MasterSpoon/Ortho66_Optical/Ortho66_Optical.kicad_sch

## KiCad design Ortho66_Optical.kicad_sch (2022-03-05)

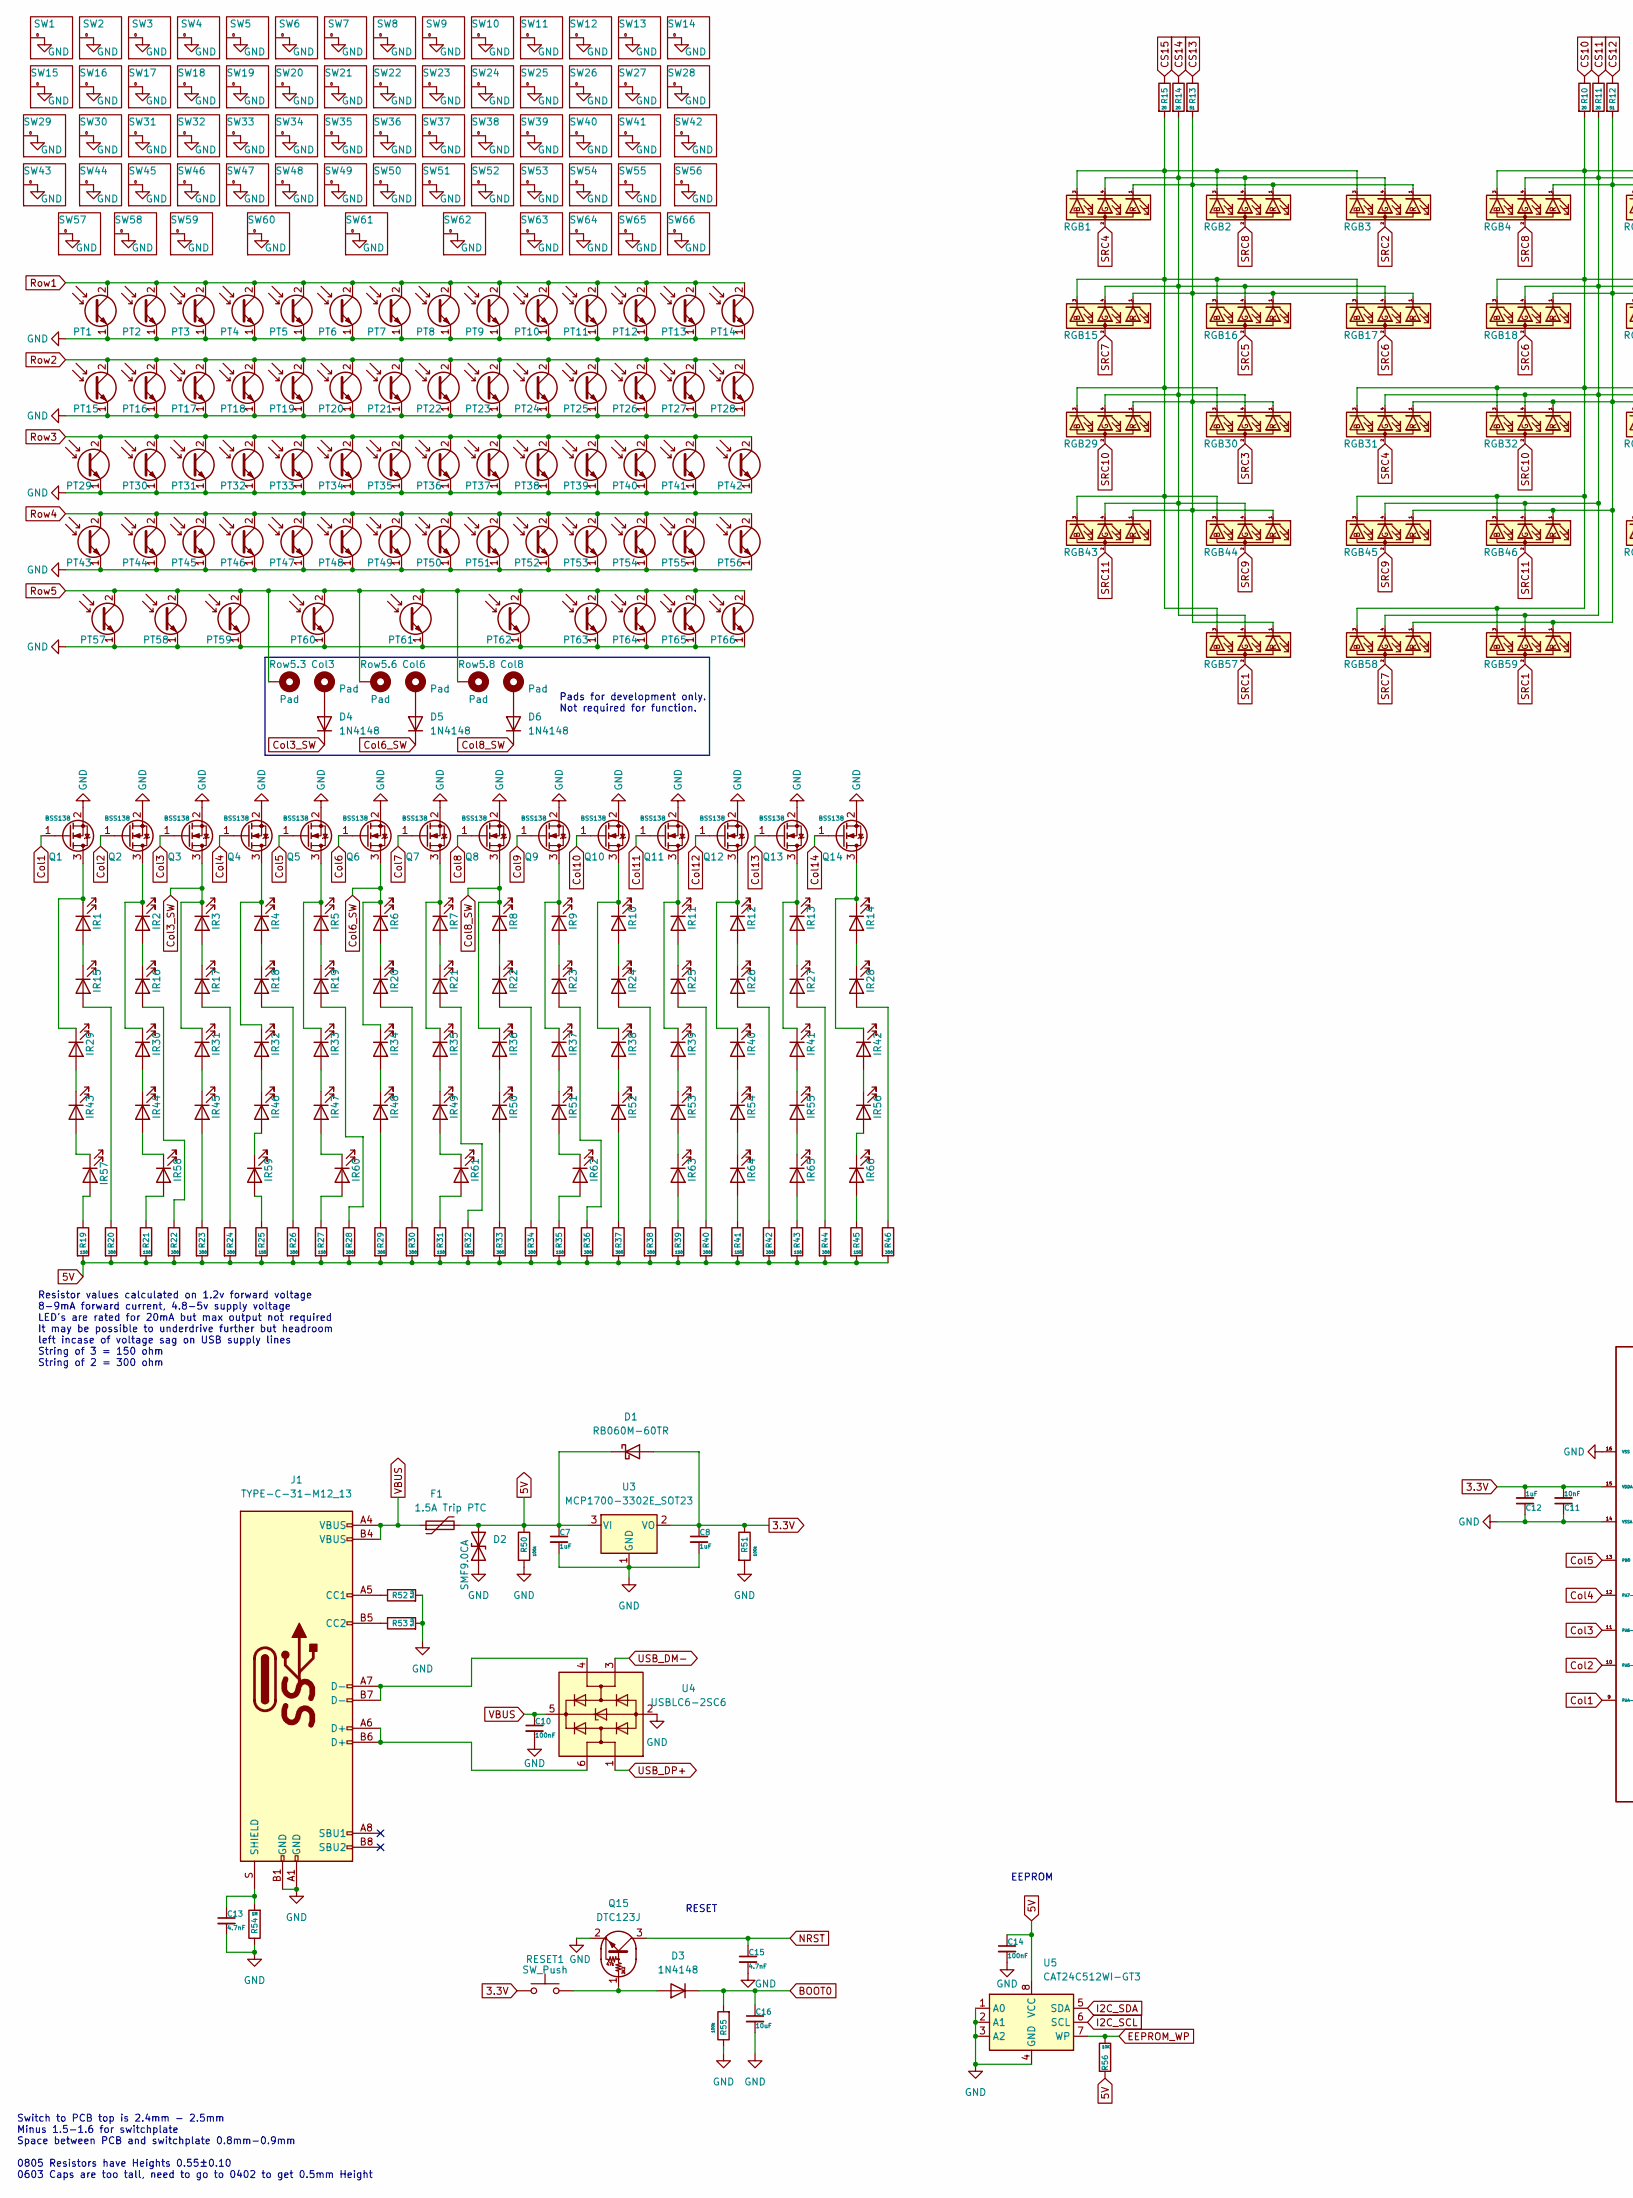
[picture p3: schematic Ortho66_Optical.kicad_sch, part in row 1, column 1]

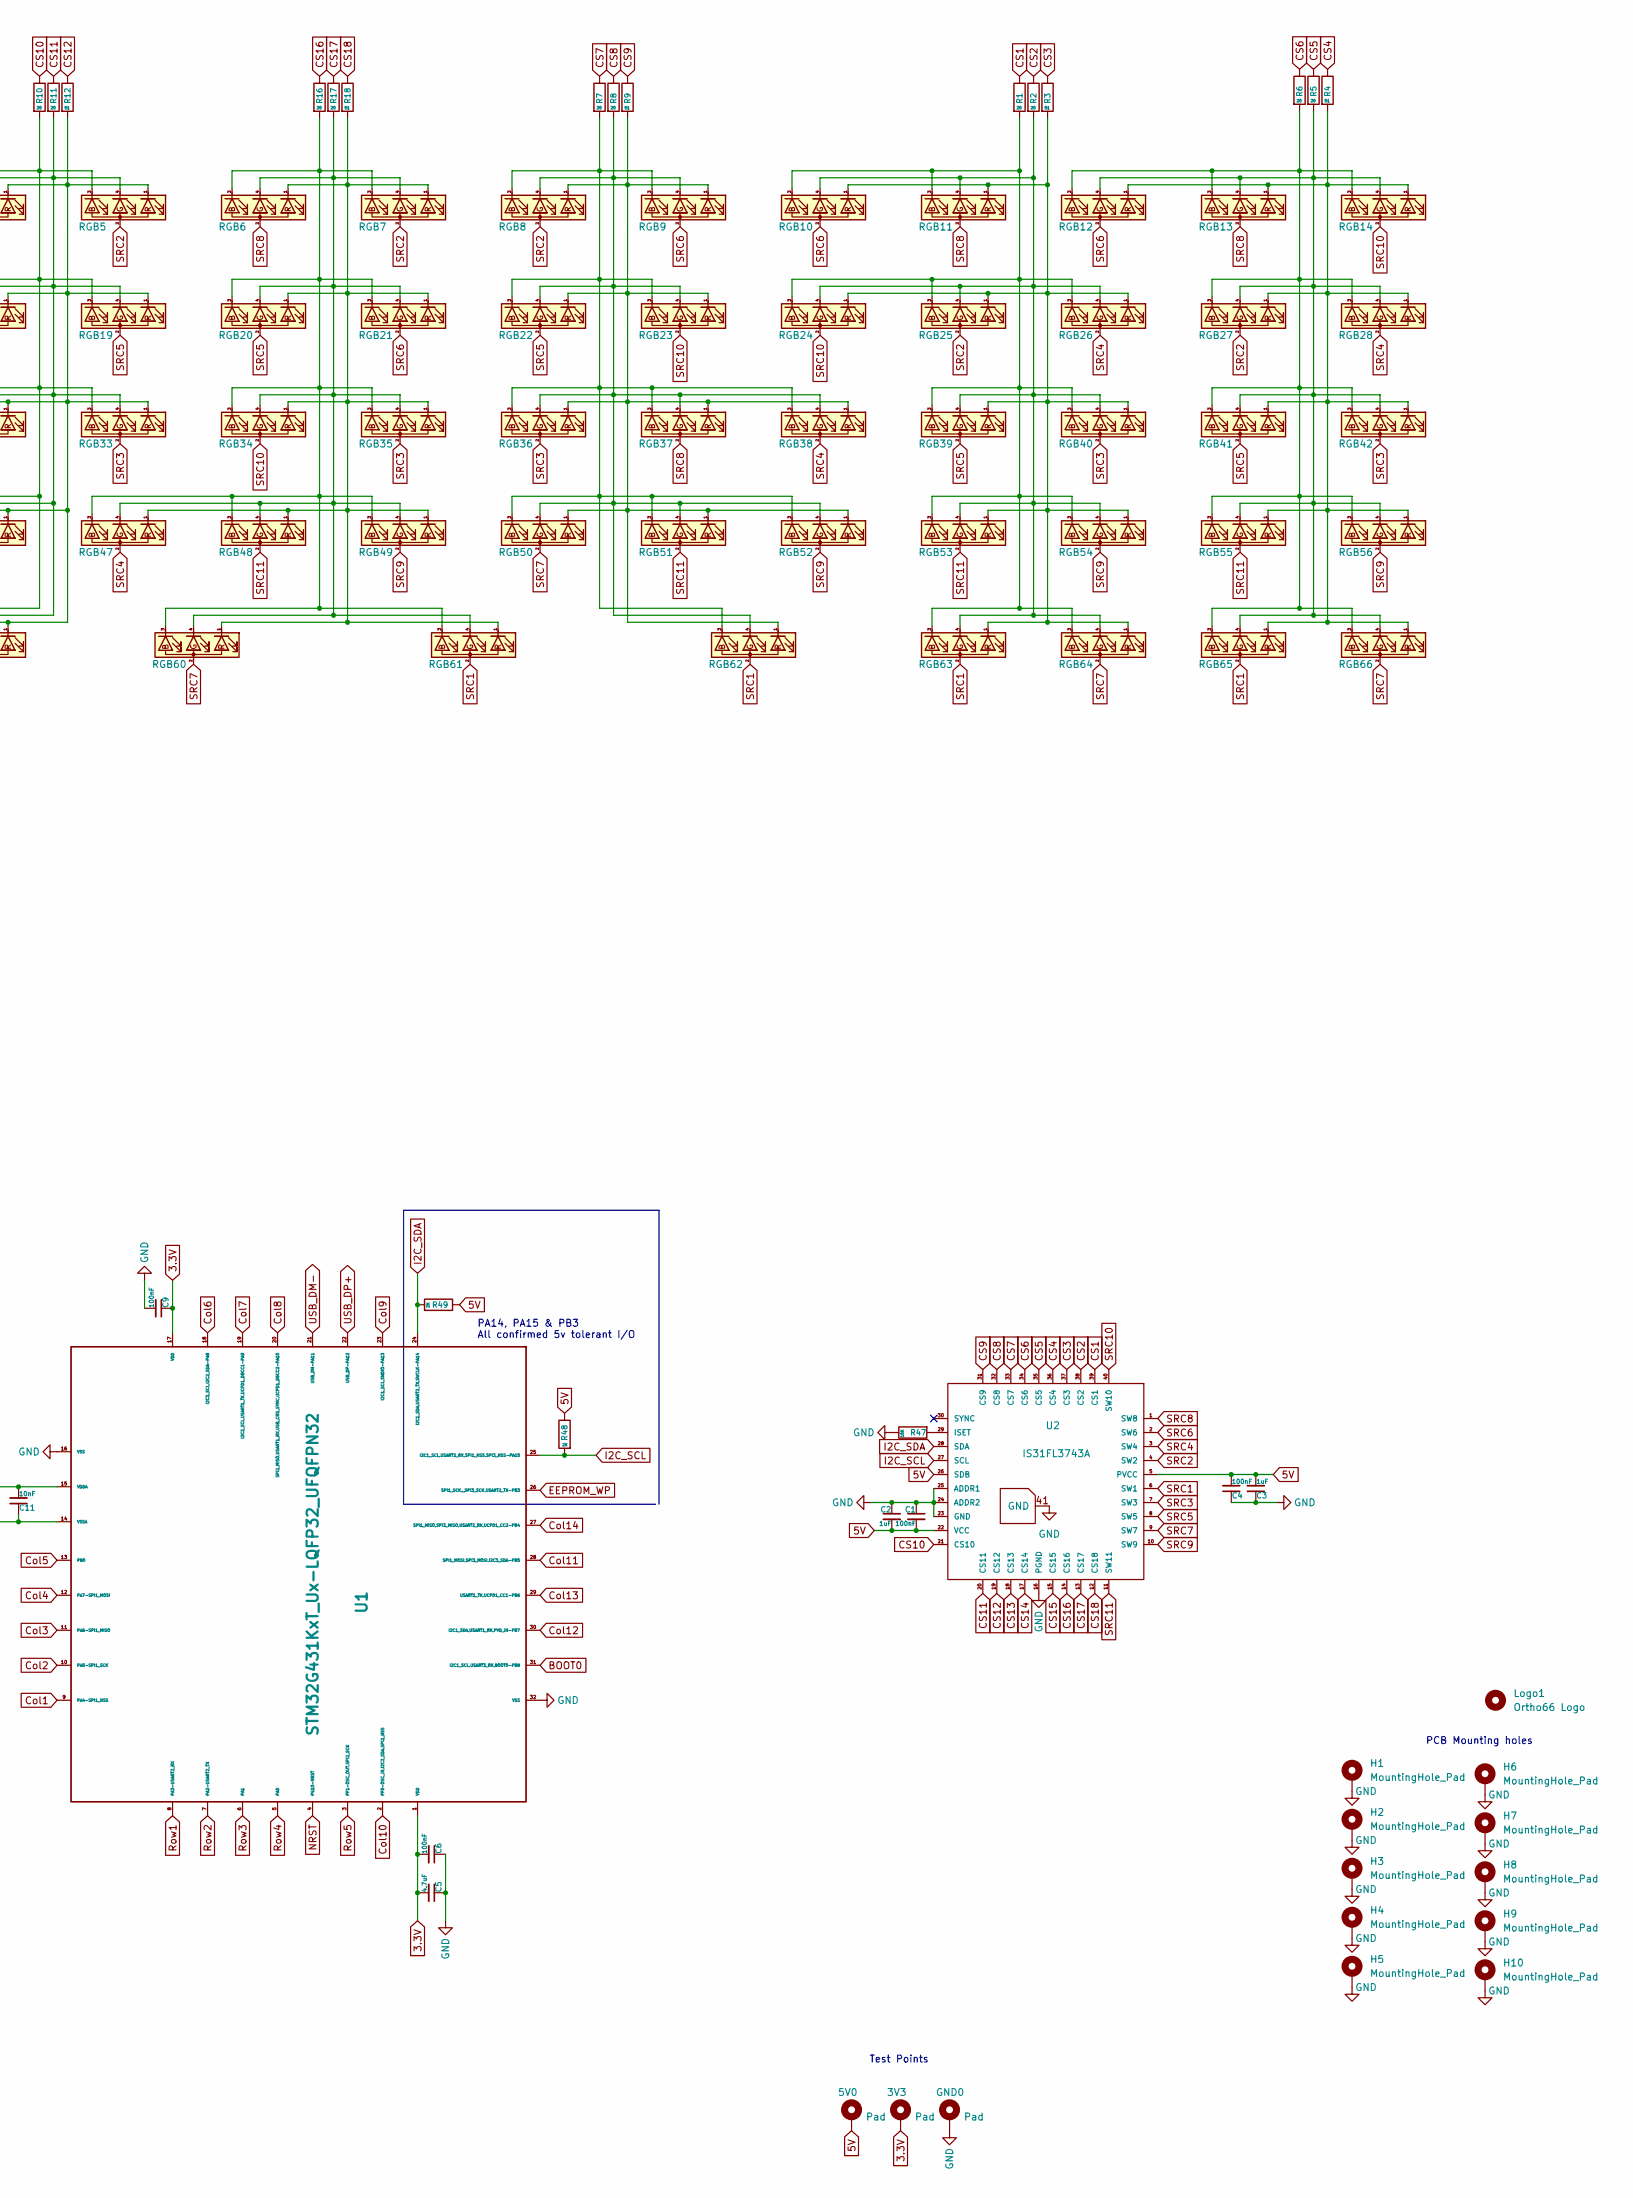
[picture p4: schematic Ortho66_Optical.kicad_sch, part in row 1, column 2]

Parts:
3V3, 5V0: Pad; SolderWirePad_1x01_SMD_1x2mm
C1, C4, C6, C9, C10, C14: 100nF; C_0402_1005Metric
C2, C3, C7, C8, C12: 1uF; C_0402_1005Metric
C5: 4.7uF; C_0402_1005Metric
C11: 10nF; C_0402_1005Metric
C13, C15: 4.7nF; C_0402_1005Metric
C16: 10uF; C_0402_1005Metric
Col3, Col6, Col8: Pad; SolderWirePad_1x01_SMD_1x2mm
D1: RB060M-60TR; D_SOD-123
D2: SMF9.0CA; D_SOD-123
D3, D4, D5, D6: 1N4148; D_SOD-123
F1: 1.5A Trip PTC; Fuse_1812_4532Metric
GND0: Pad; SolderWirePad_1x01_SMD_1x2mm
H1, H2, H3, H4, H5, H6, H7, H8, H9, H10: MountingHole_Pad; 6.2mm_mount
IR1, IR2, IR3, IR4, IR5, IR6, IR7, IR8, IR9, IR10, IR11, IR12, IR13, IR14, IR15, IR16, IR17, IR18, IR19, IR20, IR21, IR22, IR23, IR24, IR25, IR26, IR27, IR28, IR29, IR30, IR31, IR32, IR33, IR34, IR35, IR36, IR37, IR38, IR39, IR40, IR41, IR42, IR43, IR44, IR45, IR46, IR47, IR48, IR49, IR50, IR51, IR52, IR53, IR54, IR55, IR56, IR57, IR58, IR59, IR60, IR61, IR62, IR63, IR64, IR65, IR66: IR12-21C_TR8; LCSC C53672
J1: TYPE-C-31-M12_13; USB_C_Receptacle_TYPE-C-31-M-12
Logo1: Ortho66 Logo; Ortho_66_Logo
PT1, PT2, PT3, PT4, PT5, PT6, PT7, PT8, PT9, PT10, PT11, PT12, PT13, PT14, PT15, PT16, PT17, PT18, PT19, PT20, PT21, PT22, PT23, PT24, PT25, PT26, PT27, PT28, PT29, PT30, PT31, PT32, PT33, PT34, PT35, PT36, PT37, PT38, PT39, PT40, PT41, PT42, PT43, PT44, PT45, PT46, PT47, PT48, PT49, PT50, PT51, PT52, PT53, PT54, PT55, PT56, PT57, PT58, PT59, PT60, PT61, PT62, PT63, PT64, PT65, PT66: PT12-21B_TR8; LCSC C264383
Q1, Q2, Q3, Q4, Q5, Q6, Q7, Q8, Q9, Q10, Q11, Q12, Q13, Q14: BSS138; SOT-23
Q15: DTC123J; SOT-23
R1, R2, R5, R6, R7, R8, R10, R11, R14, R15, R16, R17: 20; R_0805_2012Metric
R3, R4, R9, R12, R13, R18: 51; R_0805_2012Metric
R19, R21, R25, R27, R31, R35, R39, R41, R43, R45: 150; R_0805_2012Metric
R20, R22, R23, R24, R26, R28, R29, R30, R32, R33, R34, R36, R37, R38, R40, R42, R44, R46: 300; R_0805_2012Metric
R47, R56: 10K; R_0805_2012Metric
R48, R49: 2K; R_0805_2012Metric
R50, R51, R55: 100k; R_0805_2012Metric
R52, R53: 5.1k; R_0805_2012Metric
R54: 1M; R_0805_2012Metric
RESET1: SW_Push; K2-1187SQ-A4SW-06
RGB1, RGB2, RGB4, RGB6, RGB9, RGB10, RGB13, RGB26, RGB31, RGB47: RS-1515MBAM; RS-1515MBAM-RGB_LED-TopRight; LCSC C727906
RGB3, RGB5, RGB7, RGB11, RGB14: RS-1515MBAM; RS-1515MBAM-RGB_LED-TopLeft; LCSC C727906
RGB8, RGB38: RS-1515MBAM; RS-1515MBAM-RGB_LED-Top; LCSC C727906
RGB12: RS-1515MBAM; RS-1515MBAM-RGB_LED-SW12; LCSC C727906
RGB15, RGB16, RGB18, RGB19, RGB20, RGB21, RGB22, RGB23, RGB25, RGB27, RGB30, RGB32, RGB34, RGB35, RGB36, RGB37, RGB39, RGB40, RGB41, RGB42, RGB46, RGB51, RGB53, RGB54, RGB55, RGB56: RS-1515MBAM; RS-1515MBAM-RGB_LED-Midjoin; LCSC C727906
RGB17, RGB24, RGB33, RGB64, RGB65: RS-1515MBAM; RS-1515MBAM-RGB_LED-Bott; LCSC C727906
RGB28: RS-1515MBAM; RS-1515MBAM-RGB_LED-SW28; LCSC C727906
RGB29: RS-1515MBAM; RS-1515MBAM-RGB_LED-SW29; LCSC C727906
RGB43, RGB49, RGB50: RS-1515MBAM; RS-1515MBAM-RGB_LED-Bottjoinleft; LCSC C727906
RGB44, RGB63: RS-1515MBAM; RS-1515MBAM-RGB_LED-SW63; LCSC C727906
RGB45, RGB48, RGB52: RS-1515MBAM; RS-1515MBAM-RGB_LED-Bottjoinright; LCSC C727906
RGB57, RGB61: RS-1515MBAM; RS-1515MBAM-RGB_LED-Bottleft; LCSC C727906
RGB58, RGB60, RGB62: RS-1515MBAM; RS-1515MBAM-RGB_LED-Bottright; LCSC C727906
RGB59, RGB66: RS-1515MBAM; RS-1515MBAM-RGB_LED-SW66; LCSC C727906
Row5.3, Row5.6, Row5.8: Pad; SolderWirePad_1x01_SMD_1x2mm
SW1, SW2, SW3, SW4, SW5, SW6, SW7, SW8, SW9, SW10, SW11, SW12, SW13, SW14, SW15, SW16, SW17, SW18, SW19, SW20, SW21, SW22, SW23, SW24, SW25, SW26, SW27, SW28, SW29, SW30, SW31, SW32, SW33, SW34, SW35, SW36, SW37, SW38, SW39, SW40, SW41, SW42, SW43, SW44, SW45, SW46, SW47, SW48, SW49, SW50, SW51, SW52, SW53, SW54, SW55, SW56, SW57, SW58, SW59, SW60, SW61, SW62, SW63, SW64, SW65, SW66: Keychron_LP_Optical
U1: STM32G431KxT_Ux-LQFP32_UFQFPN32; LQFP-32_7x7mm_P0.8mm
U2: IS31FL3743A; QFN-40-IS31FL3743A_0.2mmClearance
U3: MCP1700-3302E_SOT23; SOT-23
U4: USBLC6-2SC6; SOT-23-6
U5: CAT24C512WI-GT3; SOIC-8_5.23x5.23mm_P1.27mm; LCSC C79986

Connections:
3.3V: 3V3.1, C5.2, C6.2, C8.1, C9.1, C11.2, C12.2, D1.2 (A), R51.1, RESET1.2, U1.1 (VDD), U1.15 (VDDA), U1.17 (VDD), U3.2 (VO)
5V: 5V0.1, C1.2, C2.2, C3.2, C4.2, C7.1, C14.1, D1.1 (K), D2.2 (A2), F1.2, R19.2, R20.2, R21.2, R22.2, R23.2, R24.2, R25.2, R26.2, R27.2, R28.2, R29.2, R30.2, R31.2, R32.2, R33.2, R34.2, R35.2, R36.2, R37.2, R38.2, R39.2, R40.2, R41.2, R42.2, R43.2, R44.2, R45.2, R46.2, R48.1, R49.1, R50.1, R56.2, U2.5 (PVCC), U2.22 (VCC), U2.26 (SDB), U3.3 (VI), U5.8 (VCC)
BOOT0: C16.1, D3.1 (K), R55.2, U1.31 (I2C1_SCL,USART3_RX,BOOT0-PB8)
CS1: R1.1, U2.39 (CS1)
CS2: R2.1, U2.38 (CS2)
CS3: R3.1, U2.37 (CS3)
CS4: R4.1, U2.36 (CS4)
CS5: R5.1, U2.35 (CS5)
CS6: R6.1, U2.34 (CS6)
CS7: R7.1, U2.33 (CS7)
CS8: R8.1, U2.32 (CS8)
CS9: R9.1, U2.31 (CS9)
CS10: R10.1, U2.21 (CS10)
CS11: R11.1, U2.20 (CS11)
CS12: R12.1, U2.19 (CS12)
CS13: R13.1, U2.18 (CS13)
CS14: R14.1, U2.17 (CS14)
CS15: R15.1, U2.15 (CS15)
CS16: R16.1, U2.14 (CS16)
CS17: R17.1, U2.13 (CS17)
CS18: R18.1, U2.12 (CS18)
Col1: Q1.1 (G), U1.9 (PA4-SPI1_NSS)
Col2: Q2.1 (G), U1.10 (PA5-SPI1_SCK)
Col3: Q3.1 (G), U1.11 (PA6-SPI1_MISO)
Col3_SW: D4.1 (K), IR3.2 (K), IR31.2 (K), Q3.3 (D)
Col4: Q4.1 (G), U1.12 (PA7-SPI1_MOSI)
Col5: Q5.1 (G), U1.13 (PB0)
Col6: Q6.1 (G), U1.18 (I2C3_SCL,I2C2_SDA-PA8)
Col6_SW: D5.1 (K), IR6.2 (K), IR34.2 (K), Q6.3 (D)
Col7: Q7.1 (G), U1.19 (I2C2_SCL,USART1_TX,UCPD1_DBCC1-PA9)
Col8: Q8.1 (G), U1.20 (SPI2_MISO,USART1_RX,USB_CRS_SYNC,UCPD1_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)
Col8_SW: D6.1 (K), IR8.2 (K), IR36.2 (K), Q8.3 (D)
Col9: Q9.1 (G), U1.23 (I2C1_SCL,SWDIO-PA13)
Col10: Q10.1 (G), U1.2 (PF0-OSC_IN,I2C2_SDA,SPI2_NSS)
Col11: Q11.1 (G), U1.28 (SPI1_MOSI,SPI3_MOSI,I2C3_SDA-PB5)
Col12: Q12.1 (G), U1.30 (I2C1_SDA,USART1_RX,PVD_IN-PB7)
Col13: Q13.1 (G), U1.29 (USART1_TX,UCPD1_CC1-PB6)
Col14: Q14.1 (G), U1.27 (SPI1_MISO,SPI3_MISO,USART2_RX,UCPD1_CC2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)
EEPROM_WP: R56.1, U1.26 (SPI1_SCK,_SPI3_SCK,USART2_TX-PB3), U5.7 (WP)
GND: C1.1, C2.1, C3.1, C4.1, C5.1, C6.1, C7.2, C8.2, C9.2, C10.2, C11.1, C12.1, C13.2, C14.2, C15.2, C16.2, D2.1 (A1), H1.0, H2.0, H3.0, H4.0, H5.0, H6.0, H7.0, H8.0, H9.0, H10.0, J1.A1 (GND), J1.B1 (GND), PT1.1 (E), PT2.1 (E), PT3.1 (E), PT4.1 (E), PT5.1 (E), PT6.1 (E), PT7.1 (E), PT8.1 (E), PT9.1 (E), PT10.1 (E), PT11.1 (E), PT12.1 (E), PT13.1 (E), PT14.1 (E), PT15.1 (E), PT16.1 (E), PT17.1 (E), PT18.1 (E), PT19.1 (E), PT20.1 (E), PT21.1 (E), PT22.1 (E), PT23.1 (E), PT24.1 (E), PT25.1 (E), PT26.1 (E), PT27.1 (E), PT28.1 (E), PT29.1 (E), PT30.1 (E), PT31.1 (E), PT32.1 (E), PT33.1 (E), PT34.1 (E), PT35.1 (E), PT36.1 (E), PT37.1 (E), PT38.1 (E), PT39.1 (E), PT40.1 (E), PT41.1 (E), PT42.1 (E), PT43.1 (E), PT44.1 (E), PT45.1 (E), PT46.1 (E), PT47.1 (E), PT48.1 (E), PT49.1 (E), PT50.1 (E), PT51.1 (E), PT52.1 (E), PT53.1 (E), PT54.1 (E), PT55.1 (E), PT56.1 (E), PT57.1 (E), PT58.1 (E), PT59.1 (E), PT60.1 (E), PT61.1 (E), PT62.1 (E), PT63.1 (E), PT64.1 (E), PT65.1 (E), PT66.1 (E), Q1.2 (S), Q2.2 (S), Q3.2 (S), Q4.2 (S), Q5.2 (S), Q6.2 (S), Q7.2 (S), Q8.2 (S), Q9.2 (S), Q10.2 (S), Q11.2 (S), Q12.2 (S), Q13.2 (S), Q14.2 (S), Q15.2 (E), R47.1, R50.2, R51.2, R52.2, R53.2, R54.1, R55.1, SW1.0, SW2.0, SW3.0, SW4.0, SW5.0, SW6.0, SW7.0, SW8.0, SW9.0, SW10.0, SW11.0, SW12.0, SW13.0, SW14.0, SW15.0, SW16.0, SW17.0, SW18.0, SW19.0, SW20.0, SW21.0, SW22.0, SW23.0, SW24.0, SW25.0, SW26.0, SW27.0, SW28.0, SW29.0, SW30.0, SW31.0, SW32.0, SW33.0, SW34.0, SW35.0, SW36.0, SW37.0, SW38.0, SW39.0, SW40.0, SW41.0, SW42.0, SW43.0, SW44.0, SW45.0, SW46.0, SW47.0, SW48.0, SW49.0, SW50.0, SW51.0, SW52.0, SW53.0, SW54.0, SW55.0, SW56.0, SW57.0, SW58.0, SW59.0, SW60.0, SW61.0, SW62.0, SW63.0, SW64.0, SW65.0, SW66.0, U1.14 (VSSA), U1.16 (VSS), U1.32 (VSS), U2.16 (PGND), U2.23 (GND), U2.24 (ADDR2), U2.25 (ADDR1), U2.41 (GND), U3.1 (GND), U4.2 (GND), U5.1 (A0), U5.2 (A1), U5.3 (A2), U5.4 (GND)
I2C_SCL: R48.2, U1.25 (I2C1_SCL,USART2_RX,SPI1_NSS,SPI3_NSS-PA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), U2.27 (SCL), U5.6 (SCL)
I2C_SDA: R49.2, U1.24 (I2C1_SDA,USART2_TX,SWCLK-PA14), U2.28 (SDA), U5.5 (SDA)
NRST: C15.1, Q15.3 (C), U1.4 (PG10-NRST)
unnamed: C13.1, J1.S (SHIELD), R54.2
unnamed: Col3.1, D4.2 (A)
unnamed: Col6.1, D5.2 (A)
unnamed: Col8.1, D6.2 (A)
unnamed: D3.2 (A), Q15.1 (B), RESET1.1
unnamed: IR1.1 (A), IR15.2 (K)
unnamed: IR1.2 (K), IR29.2 (K), Q1.3 (D)
unnamed: IR2.2 (K), IR30.2 (K), Q2.3 (D)
unnamed: IR10.1 (A), IR24.2 (K)
unnamed: IR10.2 (K), IR38.2 (K), Q10.3 (D)
unnamed: IR11.1 (A), IR25.2 (K)
unnamed: IR11.2 (K), IR39.2 (K), Q11.3 (D)
unnamed: IR12.1 (A), IR26.2 (K)
unnamed: IR12.2 (K), IR40.2 (K), Q12.3 (D)
unnamed: IR13.1 (A), IR27.2 (K)
unnamed: IR13.2 (K), IR41.2 (K), Q13.3 (D)
unnamed: IR14.1 (A), IR28.2 (K)
unnamed: IR14.2 (K), IR42.2 (K), Q14.3 (D)
unnamed: IR15.1 (A), R20.1
unnamed: IR16.1 (A), R22.1
unnamed: IR2.1 (A), IR16.2 (K)
unnamed: IR17.1 (A), R24.1
unnamed: IR3.1 (A), IR17.2 (K)
unnamed: IR18.1 (A), R26.1
unnamed: IR4.1 (A), IR18.2 (K)
unnamed: IR19.1 (A), R28.1
unnamed: IR5.1 (A), IR19.2 (K)
unnamed: IR20.1 (A), R30.1
unnamed: IR6.1 (A), IR20.2 (K)
unnamed: IR21.1 (A), R32.1
unnamed: IR7.1 (A), IR21.2 (K)
unnamed: IR22.1 (A), R34.1
unnamed: IR8.1 (A), IR22.2 (K)
unnamed: IR23.1 (A), R36.1
unnamed: IR9.1 (A), IR23.2 (K)
unnamed: IR24.1 (A), R38.1
unnamed: IR25.1 (A), R40.1
unnamed: IR26.1 (A), R42.1
unnamed: IR27.1 (A), R44.1
unnamed: IR28.1 (A), R46.1
unnamed: IR29.1 (A), IR43.2 (K)
unnamed: IR30.1 (A), IR44.2 (K)
unnamed: IR31.1 (A), IR45.2 (K)
unnamed: IR32.1 (A), IR46.2 (K)
unnamed: IR4.2 (K), IR32.2 (K), Q4.3 (D)
unnamed: IR33.1 (A), IR47.2 (K)
unnamed: IR5.2 (K), IR33.2 (K), Q5.3 (D)
unnamed: IR34.1 (A), IR48.2 (K)
unnamed: IR35.1 (A), IR49.2 (K)
unnamed: IR7.2 (K), IR35.2 (K), Q7.3 (D)
unnamed: IR36.1 (A), IR50.2 (K)
unnamed: IR37.1 (A), IR51.2 (K)
unnamed: IR9.2 (K), IR37.2 (K), Q9.3 (D)
unnamed: IR38.1 (A), IR52.2 (K)
unnamed: IR39.1 (A), IR53.2 (K)
unnamed: IR40.1 (A), IR54.2 (K)
unnamed: IR41.1 (A), IR55.2 (K)
unnamed: IR42.1 (A), IR56.2 (K)
unnamed: IR43.1 (A), IR57.2 (K)
unnamed: IR44.1 (A), IR58.2 (K)
unnamed: IR45.1 (A), R23.1
unnamed: IR46.1 (A), IR59.2 (K)
unnamed: IR47.1 (A), IR60.2 (K)
unnamed: IR48.1 (A), R29.1
unnamed: IR49.1 (A), IR61.2 (K)
unnamed: IR50.1 (A), R33.1
unnamed: IR51.1 (A), IR62.2 (K)
unnamed: IR52.1 (A), R37.1
unnamed: IR53.1 (A), IR63.2 (K)
unnamed: IR54.1 (A), IR64.2 (K)
unnamed: IR55.1 (A), IR65.2 (K)
unnamed: IR56.1 (A), IR66.2 (K)
unnamed: IR57.1 (A), R19.1
unnamed: IR58.1 (A), R21.1
unnamed: IR59.1 (A), R25.1
unnamed: IR60.1 (A), R27.1
unnamed: IR61.1 (A), R31.1
unnamed: IR62.1 (A), R35.1
unnamed: IR63.1 (A), R39.1
unnamed: IR64.1 (A), R41.1
unnamed: IR65.1 (A), R43.1
unnamed: IR66.1 (A), R45.1
unnamed: J1.A5 (CC1), R52.1
unnamed: J1.A6 (D+), J1.B6 (D+), U4.6 (I/O1)
unnamed: J1.A7 (D-), J1.B7 (D-), U4.4 (I/O2)
unnamed: J1.B5 (CC2), R53.1
unnamed: R1.2, RGB10.3 (BK), RGB11.3 (BK), RGB24.3 (BK), RGB25.3 (BK), RGB26.3 (BK), RGB39.3 (BK), RGB40.3 (BK), RGB53.3 (BK), RGB54.3 (BK), RGB63.3 (BK), RGB64.3 (BK)
unnamed: R2.2, RGB10.4 (GK), RGB11.4 (GK), RGB24.4 (GK), RGB25.4 (GK), RGB26.4 (GK), RGB39.4 (GK), RGB40.4 (GK), RGB53.4 (GK), RGB54.4 (GK), RGB63.4 (GK), RGB64.4 (GK)
unnamed: R3.2, RGB10.1 (RK), RGB11.1 (RK), RGB24.1 (RK), RGB25.1 (RK), RGB26.1 (RK), RGB39.1 (RK), RGB40.1 (RK), RGB53.1 (RK), RGB54.1 (RK), RGB63.1 (RK), RGB64.1 (RK)
unnamed: R4.2, RGB12.1 (RK), RGB13.1 (RK), RGB14.1 (RK), RGB27.1 (RK), RGB28.1 (RK), RGB41.1 (RK), RGB42.1 (RK), RGB55.1 (RK), RGB56.1 (RK), RGB65.1 (RK), RGB66.1 (RK)
unnamed: R5.2, RGB12.4 (GK), RGB13.4 (GK), RGB14.4 (GK), RGB27.4 (GK), RGB28.4 (GK), RGB41.4 (GK), RGB42.4 (GK), RGB55.4 (GK), RGB56.4 (GK), RGB65.4 (GK), RGB66.4 (GK)
unnamed: R6.2, RGB12.3 (BK), RGB13.3 (BK), RGB14.3 (BK), RGB27.3 (BK), RGB28.3 (BK), RGB41.3 (BK), RGB42.3 (BK), RGB55.3 (BK), RGB56.3 (BK), RGB65.3 (BK), RGB66.3 (BK)
unnamed: R7.2, RGB8.3 (BK), RGB9.3 (BK), RGB22.3 (BK), RGB23.3 (BK), RGB36.3 (BK), RGB37.3 (BK), RGB38.3 (BK), RGB50.3 (BK), RGB51.3 (BK), RGB52.3 (BK), RGB62.3 (BK)
unnamed: R8.2, RGB8.4 (GK), RGB9.4 (GK), RGB22.4 (GK), RGB23.4 (GK), RGB36.4 (GK), RGB37.4 (GK), RGB38.4 (GK), RGB50.4 (GK), RGB51.4 (GK), RGB52.4 (GK), RGB62.4 (GK)
unnamed: R9.2, RGB8.1 (RK), RGB9.1 (RK), RGB22.1 (RK), RGB23.1 (RK), RGB36.1 (RK), RGB37.1 (RK), RGB38.1 (RK), RGB50.1 (RK), RGB51.1 (RK), RGB52.1 (RK), RGB62.1 (RK)
unnamed: R10.2, RGB4.3 (BK), RGB5.3 (BK), RGB18.3 (BK), RGB19.3 (BK), RGB31.3 (BK), RGB32.3 (BK), RGB33.3 (BK), RGB45.3 (BK), RGB46.3 (BK), RGB58.3 (BK), RGB59.3 (BK)
unnamed: R11.2, RGB4.4 (GK), RGB5.4 (GK), RGB18.4 (GK), RGB19.4 (GK), RGB31.4 (GK), RGB32.4 (GK), RGB33.4 (GK), RGB45.4 (GK), RGB46.4 (GK), RGB58.4 (GK), RGB59.4 (GK)
unnamed: R12.2, RGB4.1 (RK), RGB5.1 (RK), RGB18.1 (RK), RGB19.1 (RK), RGB31.1 (RK), RGB32.1 (RK), RGB33.1 (RK), RGB45.1 (RK), RGB46.1 (RK), RGB58.1 (RK), RGB59.1 (RK)
unnamed: R13.2, RGB1.1 (RK), RGB2.1 (RK), RGB3.1 (RK), RGB15.1 (RK), RGB16.1 (RK), RGB17.1 (RK), RGB29.1 (RK), RGB30.1 (RK), RGB43.1 (RK), RGB44.1 (RK), RGB57.1 (RK)
unnamed: R14.2, RGB1.4 (GK), RGB2.4 (GK), RGB3.4 (GK), RGB15.4 (GK), RGB16.4 (GK), RGB17.4 (GK), RGB29.4 (GK), RGB30.4 (GK), RGB43.4 (GK), RGB44.4 (GK), RGB57.4 (GK)
unnamed: R15.2, RGB1.3 (BK), RGB2.3 (BK), RGB3.3 (BK), RGB15.3 (BK), RGB16.3 (BK), RGB17.3 (BK), RGB29.3 (BK), RGB30.3 (BK), RGB43.3 (BK), RGB44.3 (BK), RGB57.3 (BK)
unnamed: R16.2, RGB6.3 (BK), RGB7.3 (BK), RGB20.3 (BK), RGB21.3 (BK), RGB34.3 (BK), RGB35.3 (BK), RGB47.3 (BK), RGB48.3 (BK), RGB49.3 (BK), RGB60.3 (BK), RGB61.3 (BK)
unnamed: R17.2, RGB6.4 (GK), RGB7.4 (GK), RGB20.4 (GK), RGB21.4 (GK), RGB34.4 (GK), RGB35.4 (GK), RGB47.4 (GK), RGB48.4 (GK), RGB49.4 (GK), RGB60.4 (GK), RGB61.4 (GK)
unnamed: R18.2, RGB6.1 (RK), RGB7.1 (RK), RGB20.1 (RK), RGB21.1 (RK), RGB34.1 (RK), RGB35.1 (RK), RGB47.1 (RK), RGB48.1 (RK), RGB49.1 (RK), RGB60.1 (RK), RGB61.1 (RK)
unnamed: R47.2, U2.29 (ISET)
Row1: PT1.2 (C), PT2.2 (C), PT3.2 (C), PT4.2 (C), PT5.2 (C), PT6.2 (C), PT7.2 (C), PT8.2 (C), PT9.2 (C), PT10.2 (C), PT11.2 (C), PT12.2 (C), PT13.2 (C), PT14.2 (C), U1.8 (PA3-USART2_RX)
Row2: PT15.2 (C), PT16.2 (C), PT17.2 (C), PT18.2 (C), PT19.2 (C), PT20.2 (C), PT21.2 (C), PT22.2 (C), PT23.2 (C), PT24.2 (C), PT25.2 (C), PT26.2 (C), PT27.2 (C), PT28.2 (C), U1.7 (PA2-USART2_TX)
Row3: PT29.2 (C), PT30.2 (C), PT31.2 (C), PT32.2 (C), PT33.2 (C), PT34.2 (C), PT35.2 (C), PT36.2 (C), PT37.2 (C), PT38.2 (C), PT39.2 (C), PT40.2 (C), PT41.2 (C), PT42.2 (C), U1.6 (PA1)
Row4: PT43.2 (C), PT44.2 (C), PT45.2 (C), PT46.2 (C), PT47.2 (C), PT48.2 (C), PT49.2 (C), PT50.2 (C), PT51.2 (C), PT52.2 (C), PT53.2 (C), PT54.2 (C), PT55.2 (C), PT56.2 (C), U1.5 (PA0)
Row5: PT57.2 (C), PT58.2 (C), PT59.2 (C), PT60.2 (C), PT61.2 (C), PT62.2 (C), PT63.2 (C), PT64.2 (C), PT65.2 (C), PT66.2 (C), Row5.3.1, Row5.6.1, Row5.8.1, U1.3 (PF1-OSC_OUT,SPI2_SCK)
SRC1: RGB57.2 (A), RGB59.2 (A), RGB61.2 (A), RGB62.2 (A), RGB63.2 (A), RGB65.2 (A), U2.6 (SW1)
SRC2: RGB3.2 (A), RGB5.2 (A), RGB7.2 (A), RGB8.2 (A), RGB25.2 (A), RGB27.2 (A), U2.4 (SW2)
SRC3: RGB30.2 (A), RGB33.2 (A), RGB35.2 (A), RGB36.2 (A), RGB40.2 (A), RGB42.2 (A), U2.7 (SW3)
SRC4: RGB1.2 (A), RGB26.2 (A), RGB28.2 (A), RGB31.2 (A), RGB38.2 (A), RGB47.2 (A), U2.3 (SW4)
SRC5: RGB16.2 (A), RGB19.2 (A), RGB20.2 (A), RGB22.2 (A), RGB39.2 (A), RGB41.2 (A), U2.8 (SW5)
SRC6: RGB9.2 (A), RGB10.2 (A), RGB12.2 (A), RGB17.2 (A), RGB18.2 (A), RGB21.2 (A), U2.2 (SW6)
SRC7: RGB15.2 (A), RGB50.2 (A), RGB58.2 (A), RGB60.2 (A), RGB64.2 (A), RGB66.2 (A), U2.9 (SW7)
SRC8: RGB2.2 (A), RGB4.2 (A), RGB6.2 (A), RGB11.2 (A), RGB13.2 (A), RGB37.2 (A), U2.1 (SW8)
SRC9: RGB44.2 (A), RGB45.2 (A), RGB49.2 (A), RGB52.2 (A), RGB54.2 (A), RGB56.2 (A), U2.10 (SW9)
SRC10: RGB14.2 (A), RGB23.2 (A), RGB24.2 (A), RGB29.2 (A), RGB32.2 (A), RGB34.2 (A), U2.40 (SW10)
SRC11: RGB43.2 (A), RGB46.2 (A), RGB48.2 (A), RGB51.2 (A), RGB53.2 (A), RGB55.2 (A), U2.11 (SW11)
USB_DM-: U1.21 (USB_DM-PA11), U4.3 (I/O2)
USB_DP+: U1.22 (USB_DP-PA12), U4.1 (I/O1)
VBUS: C10.1, F1.1, J1.A4 (VBUS), J1.B4 (VBUS), U4.5 (VBUS)

Notes on the sheet:
Resistor values calculated on 1.2v forward voltage 8-9mA forward current, 4.8-5v supply voltage LED's are rated for 20mA but max output not required It may be possible to underdrive further but headroom left incase of voltage sag on USB supply lines String of 3 = 150 ohm String of 2 = 300 ohm
EEPROM
Switch to PCB top is 2.4mm - 2.5mm Minus 1.5-1.6 for switchplate Space between PCB and switchplate 0.8mm-0.9mm 0805 Resistors have Heights 0.55±0.10 0603 Caps are too tall, need to go to 0402 to get 0.5mm Height
Pads for development only. Not required for function.
PCB Mounting holes
PA14, PA15 & PB3 All confirmed 5v tolerant I/O
RESET
Test Points
